Gabe-H/ME-507-Bicycle-Power-Meter/src/imu_thread.h

#ifndef IMU_THREAD_H
#define IMU_THREAD_H

#include <zephyr/kernel.h>
#include <zephyr/logging/log.h>
#include "icm40609.h"
#include "app_ipc.h"

#if !DT_NODE_EXISTS(ICM40609_NODE)
#error "No icm40609 node found in devicetree"
#endif

static void imu_thread(void);

#endif /* IMU_THREAD_H */
