Gabe-H/ME-507-Bicycle-Power-Meter/src/battery_thread.h

#ifndef BATT_MON_H
#define BATT_MON_H

#include <stdio.h>
#include <zephyr/kernel.h>
#include <zephyr/logging/log.h>
#include "max17048.h"
#include "app_ipc.h"

#if !DT_NODE_EXISTS(MAX17048_NODE)
#error "No MAX17048 battery monitor node found in devicetree"
#endif

static void battery_monitor_thread(void);

#endif /* BATT_MON_H */
